bitbarista/CaffePeso/src/Display.cpp

#include "Display.h"
#include "Scale.h"
#include "FlowRate.h"
#include "BluetoothScale.h"
#include "PowerManager.h"
#include "BatteryMonitor.h"
#include <WiFi.h>
#include "WiFiManager.h"
#include <Preferences.h>

Display::Display(uint8_t sdaPin, uint8_t sclPin, Scale* scale, FlowRate* flowRate)
    : sdaPin(sdaPin), sclPin(sclPin), scalePtr(scale), flowRatePtr(flowRate), bluetoothPtr(nullptr), powerManagerPtr(nullptr), batteryPtr(nullptr),
      messageStartTime(0), messageDuration(2000), showingMessage(false), 
      timerStartTime(0), timerPausedTime(0), timerRunning(false), timerPaused(false) {
    display = new Adafruit_SSD1306(SCREEN_WIDTH, SCREEN_HEIGHT, &Wire, OLED_RESET);
}

bool Display::begin() {
    Serial.println("Initializing display...");
    
    // Initialize I2C with custom pins
    Wire.begin(sdaPin, sclPin);
    
    // Test I2C connection first with timeout
    Serial.println("Testing I2C connection to display...");
    unsigned long startTime = millis();
    const unsigned long I2C_TIMEOUT = 3000; // 3 second timeout
    
    bool i2cResponding = false;
    Wire.beginTransmission(SCREEN_ADDRESS);
    
    // Wait for I2C response with timeout
    while (millis() - startTime < I2C_TIMEOUT) {
        if (Wire.endTransmission() == 0) {
            i2cResponding = true;
            Serial.println("I2C device found at display address");
            break;
        }
        delay(100);
        Wire.beginTransmission(SCREEN_ADDRESS);
    }
    
    if (!i2cResponding) {
        Serial.println("ERROR: No I2C device found at display address");
        Serial.println("Display will be disabled - running headless mode");
        Serial.println("Check connections:");
        Serial.printf("- SDA to GPIO %d\n", sdaPin);
        Serial.printf("- SCL to GPIO %d\n", sclPin);
        Serial.println("- VCC to 3.3V");
        Serial.println("- GND to GND");
        displayConnected = false;
        return false;
    }
    
    // Initialize the display
    if (!display->begin(SSD1306_SWITCHCAPVCC, SCREEN_ADDRESS)) {
        Serial.println("ERROR: SSD1306 initialization failed");
        Serial.println("Display will be disabled - running headless mode");
        displayConnected = false;
        return false;
    }
    
    Serial.println("Display connected and initialized successfully");
    displayConnected = true;
    setupDisplay();
    
    // Show startup message in same format as welcome message
    display->clearDisplay();
    display->setTextSize(2);
    display->setTextColor(SSD1306_WHITE);
    
    String line1 = "CaffePeso";
    String line2 = "Starting";
    
    int16_t x1, y1;
    uint16_t w1, h1, w2, h2;
    
    display->getTextBounds(line1, 0, 0, &x1, &y1, &w1, &h1);
    display->getTextBounds(line2, 0, 0, &x1, &y1, &w2, &h2);
    int centerX1 = (SCREEN_WIDTH - w1) / 2;
    int centerX2 = (SCREEN_WIDTH - w2) / 2;

    display->setCursor(centerX1, 0);
    display->print(line1);
    display->setCursor(centerX2, 16);
    display->print(line2);
    
    display->display();
    
    Serial.println("SSD1306 display initialized on SDA:" + String(sdaPin) + " SCL:" + String(sclPin));
    
    return true;
}

void Display::setupDisplay() {
    // Return early if display is not connected
    if (!displayConnected) {
        return;
    }
    
    display->clearDisplay();
    display->setTextColor(SSD1306_WHITE);
    display->cp437(true); // Use full 256 char 'Code Page 437' font
}

void Display::update() {
    // Return early if display is not connected
    if (!displayConnected) {
        return;
    }
    
    // Check if message duration has elapsed
    if (showingMessage) {
        int effectiveDuration = messageDuration;
        // Use shorter duration for tared message
        if (currentMessage == "Tared message") {
            effectiveDuration = 1000; // Half of default duration for quick feedback
        }
        
        if (millis() - messageStartTime > effectiveDuration) {
            showingMessage = false;
            Serial.println("Message cleared, returning to main display");

        }
    }
    
    // Auto re-arm: tare + arm when a cup is detected after the previous shot.
    // Two detection paths:
    //   Case 1 (tap-tare workflow): user tap-tares after removing cup; fresh cup reads
    //           ≈ savedTareWeight because the tare reference is now at empty-scale.
    //   Case 2 (direct placement): user removes cup after shot (scale goes very negative),
    //           then places fresh cup directly — no tap-tare needed. Scale reads ≈ 0g
    //           because the original cup-tare reference is still intact.
    //           scaleWentNegative guards against false triggers on empty scale.
    if (scalePtr != nullptr && savedTareWeight > 5.0f && autoReArmEnabled) {
        bool activeBrew = timerRunning && !timerPaused;
        float weightNow = scalePtr->getCurrentWeight();

        // Track cup removal: set flag when scale goes deeply negative while paused
        if (timerPaused && weightNow < -(savedTareWeight * 0.5f)) {
            scaleWentNegative = true;
        }

        // Tared path: require a step change to START the stable timer.
        // Uses reArmStableSince itself as the gate:
        //   - timer not yet running + first entry into window → require step ≥ threshold
        //   - timer already running (entered via valid step) → keep it going
        //   - in window but timer never started (gradual approach) → stay blocked
        // This prevents milk being poured gradually through the cup weight from triggering re-arm.
        bool cupInWindow  = fabsf(weightNow - savedTareWeight) <= REARM_STABLE_WINDOW;
        bool prevInWindow = fabsf(prevWeightForRemoval - savedTareWeight) <= REARM_STABLE_WINDOW;
        bool cupDetectedTared;
        if (!cupInWindow) {
            cupDetectedTared = false;
        } else if (reArmStableSince != 0) {
            cupDetectedTared = true;                                     // timer running — keep going
        } else if (!prevInWindow) {
            cupDetectedTared = (weightNow - prevWeightForRemoval) >= REARM_STEP_THRESHOLD; // first entry
        } else {
            cupDetectedTared = false;                                    // gradual approach — blocked
        }
        bool cupDetectedDirect = scaleWentNegative && fabsf(weightNow) < REARM_DIRECT_WINDOW;
        bool cupDetected = cupDetectedTared || cupDetectedDirect;

        if (!activeBrew && cupDetected) {
            if (reArmStableSince == 0) reArmStableSince = millis();
            else if (millis() - reArmStableSince >= REARM_STABLE_MS) {
                reArmStableSince = 0;
                resetTimer();               // snap display to 0:00 before tare blocks
                scalePtr->tare();
                arm(savedTareWeight);
                resetTimer();               // stop that timer — auto re-arm waits for first drip
                                            // armedAutoStart is NOT cleared by resetTimer()
                showArmedMessage();
                Serial.printf("Auto re-armed: cup %.1fg detected\n", savedTareWeight);
            }
        } else {
            reArmStableSince = 0;
        }
    }

    if (!showingMessage && scalePtr != nullptr) {
        float weight = scalePtr->getCurrentWeight();

        // --- Auto-tare on vessel placement ---
        // autoTareFired is reset in resetTimer() so it fires at most once per brew cycle,
        // preventing a re-tare mid-brew when yield crosses the same threshold.
        if (autoTareEnabled) {
            float absW = fabs(weight);
            // Suppress auto-tare while the sleep/power button is held. Pressing the button
            // can transfer mechanical force through the device structure to the load cell,
            // causing a spurious reading above the threshold.
            bool sleepButtonHeld = powerManagerPtr && powerManagerPtr->isSleepTouchPressed();
            if (sleepButtonHeld) {
                autoTareStableSince = 0; // reset stability timer — don't let it accumulate while held
            } else if (weight < -2.0f) {
                autoTareStableSince = 0;
                autoTareFired = false;   // Scale went negative — vessel removed, allow auto-tare on next placement
            } else if (absW < 2.0f) {
                autoTareStableSince = 0; // Weight near zero — vessel just got tared, keep autoTareFired locked
            } else if (weight > autoTareThreshold && !autoTareFired && !timerRunning && !armedAutoStart) {
                // Only fire on positive weight — negative weight means a vessel was removed,
                // not placed. Using fabs() here caused auto-tare to trigger on large negative
                // readings (e.g. after removing a jug) which then fired again after a tap-tare.
                if (autoTareStableSince == 0) {
                    autoTareStableSince = millis();
                } else if (millis() - autoTareStableSince >= AUTO_TARE_STABLE_MS) {
                    autoTareStableSince = 0;
                    showTaringMessage();
                    scalePtr->tare();
                    resetTimer();                        // resets autoTareFired to false
                    autoTareFired = true;                // re-lock after reset so brew crossing won't re-tare
                    if (flowRatePtr) flowRatePtr->resetTimerAveraging();
                    showTaredMessage(true); // inverted to match auto re-arm visual style
                    weight = 0.0f; // reflect post-tare state immediately
                }
            } else if (weight <= autoTareThreshold) {
                autoTareStableSince = 0;
            }
        }

        // --- Post-brew idle reset ---
        // timerPaused=true after stopTimer() (timerRunning stays true); fire on paused state only.
        if (idleResetEnabled && timerPaused) {
            if (idleResetWeightStableFrom == 0) {
                idleResetWeightStableFrom = millis();
                idleResetLastWeight = weight;
            } else if (fabs(weight - idleResetLastWeight) > 0.5f) {
                idleResetWeightStableFrom = millis();
                idleResetLastWeight = weight;
            } else if (millis() - idleResetWeightStableFrom >= idleResetTimeout) {
                resetTimer();
                if (!autoReArmEnabled) {
                    // Only tare if cup re-arm is disabled — taring with cup re-arm enabled
                    // corrupts the HX711 reference and prevents re-arm from detecting the cup.
                    scalePtr->tare();
                    weight = 0.0f;
                }
                idleResetWeightStableFrom = 0;
            }
        } else if (!timerPaused) {
            idleResetWeightStableFrom = 0;
        }

        // --- Auto-zero drift correction ---
        // When idle (timer stopped) and weight has been within ±0.3g for 10s, re-tare to
        // correct slow thermal/creep drift. Keeps the zero reference accurate between brews
        // without a visible snap. The 10s window is short enough that corrections happen while
        // drift is still imperceptibly small (<0.05g typically).
        if (!timerRunning && scalePtr != nullptr) {
            if (fabsf(weight) < 0.3f && fabsf(weight) > 0.01f) {
                if (autoZeroStableSince == 0) {
                    autoZeroStableSince = millis();
                } else if (millis() - autoZeroStableSince >= AUTO_ZERO_STABLE_MS) {
                    autoZeroStableSince = 0;
                    float drift = weight;
                    scalePtr->tare();
                    weight = 0.0f;
                    Serial.printf("Auto-zero: drift corrected (was %.3fg)\n", drift);
                }
            } else {
                autoZeroStableSince = 0;
            }
        } else {
            autoZeroStableSince = 0;
        }

        // Cup removal auto-stop — if weight drops faster than any natural flow could cause,
        // the cup has been lifted; stop the timer and preserve stats
        currentWeightForCapture = weight;
        if (timerRunning && !timerPaused) {
            float weightDelta = weight - prevWeightForRemoval;
            if (prevWeightForRemoval > 5.0f && weightDelta < -CUP_REMOVAL_THRESHOLD) {
                stopTimer();
                Serial.println("Cup removal detected — timer stopped");
            }
        }
        prevWeightForRemoval = weight;

        // Armed auto-start: trigger timer when weight increases > threshold sustained 500ms.
        // Guarded against vessel placement: espresso flow rises gradually (<~0.5g per
        // 100ms cycle), whereas placing a jug/cup jumps many grams in a single cycle.
        // A step >= REARM_STEP_THRESHOLD (8g/cycle = 80g/s, impossible for coffee) is
        // treated as a placement and blocks auto-start until the weight returns to
        // baseline (vessel removed or re-tared), so e.g. weighing milk won't start the timer.
        if (armedAutoStart && !timerRunning) {
            float armStep = weight - prevWeightForArm;
            if (armStep >= REARM_STEP_THRESHOLD) {
                armBlockedByPlacement = true;          // a vessel was just placed
                armWeightAboveThresholdSince = 0;
            } else if (weight <= ARM_TRIGGER_THRESHOLD) {
                armBlockedByPlacement = false;         // back to baseline — re-allow flow detection
            }

            if (millis() - armStartedAt > ARM_TIMEOUT_MS) {
                disarm();
                Serial.println("Armed auto-start: timed out");
            } else if (weight > ARM_TRIGGER_THRESHOLD && !armBlockedByPlacement) {
                if (armWeightAboveThresholdSince == 0) {
                    armWeightAboveThresholdSince = millis();
                } else if (millis() - armWeightAboveThresholdSince >= ARM_SUSTAIN_MS) {
                    if (timerPaused) resetTimer();
                    startTimer();
                    disarm();
                    Serial.println("Armed auto-start: timer started on weight increase");
                }
            } else {
                armWeightAboveThresholdSince = 0;
            }
        }
        prevWeightForArm = weight;

        // Auto-stop on flow cessation
        if (autoStopEnabled && timerRunning && !timerPaused && flowRatePtr != nullptr) {
            float fr = flowRatePtr->getFlowRate();
            unsigned long elapsed = millis() - timerStartTime;
            if (fr > AUTO_STOP_ACTIVE_THRESHOLD) {
                autoStopFlowWasActive = true;
                autoStopBelowThresholdSince = 0;
            } else if (autoStopFlowWasActive && fr < AUTO_STOP_CEASE_THRESHOLD && elapsed > AUTO_STOP_MIN_BREW_MS) {
                if (autoStopBelowThresholdSince == 0) {
                    autoStopBelowThresholdSince = millis();
                } else if (millis() - autoStopBelowThresholdSince >= AUTO_STOP_SUSTAIN_MS) {
                    stopTimer();
                    autoStopBelowThresholdSince = 0;
                    Serial.println("Auto-stop: flow ceased");
                }
            } else if (fr >= AUTO_STOP_CEASE_THRESHOLD) {
                autoStopBelowThresholdSince = 0;
            }
        }

        // Target yield alert: invert display for 1s when approaching target yield
        if (timerRunning && !timerPaused && doseWeight > 0.5f && targetRatio > 0.0f && !alertFired) {
            float alertThreshold = doseWeight * targetRatio - 2.0f;
            if (alertThreshold > 0.0f && weight >= alertThreshold) {
                alertFired = true;
                alertFlashActive = true;
                alertFlashStart = millis();
                Serial.printf("Target yield alert: %.1fg >= threshold %.1fg\n", weight, alertThreshold);
            }
        }
        if (alertFlashActive) {
            if (millis() - alertFlashStart < ALERT_FLASH_MS) {
                display->invertDisplay(true);
            } else {
                display->invertDisplay(false);
                alertFlashActive = false;
            }
        }

        showWeightWithFlowAndTimer(weight);
    }
}

void Display::showWeight(float weight) {
    // Return early if display is not connected
    if (!displayConnected) {
        return;
    }

    if (showingMessage) return; // Don't override messages
    
    // Use the unified display showing weight, flow rate, and timer
    showWeightWithFlowAndTimer(weight);
}

void Display::showMessage(const String& message, int duration) {
    // Return early if display is not connected
    if (!displayConnected) {
        return;
    }
    
    currentMessage = message;
    messageStartTime = millis();
    messageDuration = duration; // Store the duration
    showingMessage = true;
    
    display->clearDisplay();
    display->setTextSize(1);
    display->setCursor(0, 0);
    
    // Word wrap for longer messages
    int lineHeight = 8;
    int maxCharsPerLine = 21; // For 128px width
    int currentLine = 0;
    
    for (int i = 0; i < message.length() && currentLine < 4; i += maxCharsPerLine) {
        String line = message.substring(i, min(i + maxCharsPerLine, (int)message.length()));
        display->setCursor(0, currentLine * lineHeight);
        display->print(line);
        currentLine++;
    }
    
    display->display();
}

void Display::showBatteryLowMessage(float voltage, int duration) {
    // Return early if display is not connected
    if (!displayConnected) {
        return;
    }
    
    display->clearDisplay();
    display->setTextSize(2);
    display->setTextColor(SSD1306_WHITE);
    
    String line1 = "Bat Low";
    String line2 = String(voltage, 1) + "V";
    
    int16_t x1, y1;
    uint16_t w1, h1, w2, h2;
    
    display->getTextBounds(line1, 0, 0, &x1, &y1, &w1, &h1);
    display->getTextBounds(line2, 0, 0, &x1, &y1, &w2, &h2);
    int centerX1 = (SCREEN_WIDTH - w1) / 2;
    int centerX2 = (SCREEN_WIDTH - w2) / 2;

    display->setCursor(centerX1, 0);
    display->print(line1);
    display->setCursor(centerX2, 16);
    display->print(line2);
    
    display->display();
    
    // Set message state for auto-clearing
    currentMessage = line1 + " " + line2;
    messageStartTime = millis();
    messageDuration = duration;
    showingMessage = true;
}

void Display::showSleepCountdown(int seconds) {
    // Return early if display is not connected
    if (!displayConnected) {
        return;
    }
    
    // Set message state to prevent weight display interference
    currentMessage = "Sleep countdown active";
    messageStartTime = millis();
    showingMessage = true;
    
    display->clearDisplay();
    display->setTextSize(2);
    display->setTextColor(SSD1306_WHITE);
    
    String line1 = "Sleep in";
    String line2 = String(seconds) + "...";
    
    int16_t x1, y1;
    uint16_t w1, h1, w2, h2;
    
    display->getTextBounds(line1, 0, 0, &x1, &y1, &w1, &h1);
    display->getTextBounds(line2, 0, 0, &x1, &y1, &w2, &h2);
    int centerX1 = (SCREEN_WIDTH - w1) / 2;
    int centerX2 = (SCREEN_WIDTH - w2) / 2;

    display->setCursor(centerX1, 0);
    display->print(line1);
    display->setCursor(centerX2, 16);
    display->print(line2);
    
    display->display();
}

void Display::showSleepMessage() {
    // Return early if display is not connected
    if (!displayConnected) {
        return;
    }
    
    // Set message state to prevent weight display interference
    currentMessage = "Sleep message active";
    messageStartTime = millis();
    showingMessage = true;
    
    // Large top line, small bottom line (different sizes so handled separately)
    display->clearDisplay();
    display->setTextColor(SSD1306_WHITE);
    display->setTextSize(2);
    String line1 = "Sleeping..";
    
    int16_t x1, y1;
    uint16_t w1, h1;
    display->getTextBounds(line1, 0, 0, &x1, &y1, &w1, &h1);
    int centerX1 = (SCREEN_WIDTH - w1) / 2;
    
    display->setCursor(centerX1, 0);
    display->print(line1);
    
    display->setTextSize(1);
    String line2 = "Touch to cancel";
    uint16_t w2, h2;
    display->getTextBounds(line2, 0, 0, &x1, &y1, &w2, &h2);
    int centerX2 = (SCREEN_WIDTH - w2) / 2;
    display->setCursor(centerX2, 24); // size-1 text at bottom row
    display->print(line2);
    
    display->display();
}

void Display::showGoingToSleepMessage() {
    // Return early if display is not connected
    if (!displayConnected) {
        return;
    }
    
    // Set message state to prevent weight display interference
    currentMessage = "Going to sleep message";
    messageStartTime = millis();
    showingMessage = true;
    
    display->clearDisplay();
    display->setTextSize(2);
    display->setTextColor(SSD1306_WHITE);
    String line1 = "Touch To";
    String line2 = "Wake Up";
    
    int16_t x1, y1;
    uint16_t w1, h1, w2, h2;
    
    display->getTextBounds(line1, 0, 0, &x1, &y1, &w1, &h1);
    display->getTextBounds(line2, 0, 0, &x1, &y1, &w2, &h2);
    int centerX1 = (SCREEN_WIDTH - w1) / 2;
    int centerX2 = (SCREEN_WIDTH - w2) / 2;

    display->setCursor(centerX1, 0);
    display->print(line1);
    display->setCursor(centerX2, 16);
    display->print(line2);
    
    display->display();
}

void Display::showSleepCancelledMessage() {
    // Return early if display is not connected
    if (!displayConnected) {
        return;
    }
    
    // Set message state to prevent weight display interference
    currentMessage = "Sleep cancelled message";
    messageStartTime = millis();
    showingMessage = true;
    
    display->clearDisplay();
    display->setTextSize(2);
    display->setTextColor(SSD1306_WHITE);
    String line1 = "Sleep";
    String line2 = "Cancelled";
    
    int16_t x1, y1;
    uint16_t w1, h1, w2, h2;
    
    display->getTextBounds(line1, 0, 0, &x1, &y1, &w1, &h1);
    display->getTextBounds(line2, 0, 0, &x1, &y1, &w2, &h2);
    int centerX1 = (SCREEN_WIDTH - w1) / 2;
    int centerX2 = (SCREEN_WIDTH - w2) / 2;

    display->setCursor(centerX1, 0);
    display->print(line1);
    display->setCursor(centerX2, 16);
    display->print(line2);
    
    display->display();
}

void Display::showTaringMessage() {
    // Return early if display is not connected
    if (!displayConnected) {
        return;
    }
    
    // Set message state to prevent weight display interference
    currentMessage = "Taring message";
    messageStartTime = millis();
    showingMessage = true;
    
    display->clearDisplay();
    display->setTextSize(2);
    display->setTextColor(SSD1306_WHITE);
    String line1 = "Taring";
    String line2 = "...";
    
    int16_t x1, y1;
    uint16_t w1, h1, w2, h2;
    
    display->getTextBounds(line1, 0, 0, &x1, &y1, &w1, &h1);
    display->getTextBounds(line2, 0, 0, &x1, &y1, &w2, &h2);
    int centerX1 = (SCREEN_WIDTH - w1) / 2;
    int centerX2 = (SCREEN_WIDTH - w2) / 2;

    display->setCursor(centerX1, 0);
    display->print(line1);
    display->setCursor(centerX2, 16);
    display->print(line2);
    
    display->display();
}

void Display::showReleaseMessage() {
    if (!displayConnected) return;

    currentMessage   = "Release message";
    messageStartTime = millis();
    messageDuration  = 5000; // stays until overridden by next message
    showingMessage   = true;

    display->clearDisplay();
    display->setTextSize(2);
    display->setTextColor(SSD1306_WHITE);
    String line1 = "Release";
    String line2 = "Now!";
    int16_t x1, y1;
    uint16_t w1, h1, w2, h2;
    display->getTextBounds(line1, 0, 0, &x1, &y1, &w1, &h1);
    display->getTextBounds(line2, 0, 0, &x1, &y1, &w2, &h2);
    display->setCursor((SCREEN_WIDTH - w1) / 2, 0);
    display->print(line1);
    display->setCursor((SCREEN_WIDTH - w2) / 2, 16);
    display->print(line2);
    display->display();
}

void Display::showTaredMessage(bool inverted) {
    // Return early if display is not connected
    if (!displayConnected) {
        return;
    }

    // Set message state to prevent weight display interference
    currentMessage = "Tared message";
    messageStartTime = millis();
    showingMessage = true;

    if (inverted) {
        display->fillScreen(SSD1306_WHITE);
        display->setTextColor(SSD1306_BLACK);
    } else {
        display->clearDisplay();
        display->setTextColor(SSD1306_WHITE);
    }

    // "Tared!" prominent in size 2
    display->setTextSize(2);
    String line1 = "Tared!";
    int16_t x1, y1;
    uint16_t w1, h1;
    display->getTextBounds(line1, 0, 0, &x1, &y1, &w1, &h1);
    display->setCursor((SCREEN_WIDTH - w1) / 2, 0);
    display->print(line1);

    // Hint in size 1 at bottom
    display->setTextSize(1);
    const char* hint = (savedTareWeight > 5.0f && autoReArmEnabled)
                     ? "Place cup: arm"
                     : "Hold tare: arm";
    uint16_t wh, hh;
    display->getTextBounds(hint, 0, 0, &x1, &y1, &wh, &hh);
    display->setCursor((SCREEN_WIDTH - wh) / 2, 24);
    display->print(hint);

    display->display();
    display->setTextColor(SSD1306_WHITE); // restore for subsequent draws
}


void Display::clearMessageState() {
    showingMessage = false;
    currentMessage = "";
    messageStartTime = 0;
}

void Display::showIPAddresses() {
    // Return early if display is not connected
    if (!displayConnected) {
        return;
    }

    display->clearDisplay();
    display->setTextColor(SSD1306_WHITE);

    // Top row: project name (size 2, centred)
    display->setTextSize(2);
    String name = "CaffePeso";
    int16_t x1, y1;
    uint16_t w, h;
    display->getTextBounds(name, 0, 0, &x1, &y1, &w, &h);
    display->setCursor((SCREEN_WIDTH - w) / 2, 0);
    display->print(name);

    // Bottom row: IP address (size 1, centred) — STA IP if connected, AP IP otherwise
    display->setTextSize(1);
    String ip = (WiFi.status() == WL_CONNECTED)
        ? WiFi.localIP().toString()
        : WiFi.softAPIP().toString();
    display->getTextBounds(ip, 0, 0, &x1, &y1, &w, &h);
    display->setCursor((SCREEN_WIDTH - w) / 2, 24);
    display->print(ip);

    display->display();
    delay(2000);
}

void Display::showFirstRunHint() {
    // First-run guidance: only the gesture that unlocks the hands-free workflow.
    // Draws explicit size-1 lines (showMessage's auto-wrap can't do clean line
    // breaks) but sets the message-state flags so update() auto-expires it back
    // to the live weight screen. Caller gates this on a genuine first run.
    if (!displayConnected) return;

    currentMessage   = "First run hint";
    messageStartTime = millis();
    messageDuration  = 4000;
    showingMessage   = true;

    display->clearDisplay();
    display->setTextColor(SSD1306_WHITE);
    display->setTextSize(1);
    const char* lines[] = { "Welcome to CaffePeso", "Hold the tare pad to", "tare + arm, then", "pull your first shot" };
    for (int i = 0; i < 4; i++) {
        display->setCursor(0, i * 8);
        display->print(lines[i]);
    }
    display->display();
}

void Display::clear() {
    // Return early if display is not connected
    if (!displayConnected) {
        return;
    }

    display->clearDisplay();
    display->display();
}

void Display::setBrightness(uint8_t brightness) {
    // Return early if display is not connected
    if (!displayConnected) {
        return;
    }
    
    // SSD1306 doesn't have brightness control, but we can simulate with contrast
    display->ssd1306_command(SSD1306_SETCONTRAST);
    display->ssd1306_command(brightness);
}

void Display::setBluetoothScale(BluetoothScale* bluetooth) {
    bluetoothPtr = bluetooth;
}

void Display::setPowerManager(PowerManager* powerManager) {
    powerManagerPtr = powerManager;
}

void Display::setBatteryMonitor(BatteryMonitor* battery) {
    batteryPtr = battery;
}


void Display::drawBluetoothStatus() {
    // Return early if display is not connected
    if (!displayConnected) {
        return;
    }
    
    // Only draw when connected — no indicator when scanning/disconnected
    if (bluetoothPtr && bluetoothPtr->isConnected()) {
        display->setTextSize(1);
        display->setCursor(115, 0);
        display->print("BT");
        display->drawRect(113, 0, 15, 9, SSD1306_WHITE);
    }
}

void Display::drawBatteryStatus() {
    // Return early if display is not connected or no battery monitor
    if (!displayConnected || !batteryPtr) {
        return;
    }
    
    // Get battery percentage and critical status
    int batteryPercentage = batteryPtr->getBatteryPercentage();
    bool isCritical = batteryPtr->isCriticalBattery();
    
    // Format percentage string
    String percentStr = String(batteryPercentage) + "%";
    
    // Set small text size for percentage display
    display->setTextSize(1);
    
    // For critical battery, make it flash (every 500ms)
    if (isCritical && (millis() % 1000 < 500)) {
        // Flash state - draw text with inverted colors (black text on white background)
        int16_t x1, y1;
        uint16_t textWidth, textHeight;
        display->getTextBounds(percentStr, 0, 0, &x1, &y1, &textWidth, &textHeight);
        
        // Fill background white and draw black text
        display->fillRect(0, 0, textWidth + 2, textHeight + 2, SSD1306_WHITE);
        display->setTextColor(SSD1306_BLACK);
        display->setCursor(1, 1);
        display->print(percentStr);
        display->setTextColor(SSD1306_WHITE); // Reset text color
    } else {
        // Normal percentage display in top-left corner
        display->setCursor(0, 0);
        display->print(percentStr);
    }
}

// Layout (128x32):
//   y=0..15  (16px): weight size 2, centred
//   y=16..23 ( 8px): gap
//   y=24..31 ( 8px): timer+"T" left | running ratio centre | flow right
//                    (centre ratio only when timer running and dose set;
//                     right shows final ratio when paused, flow otherwise)
void Display::showWeightWithFlowAndTimer(float weight) {
    if (!displayConnected) return;
    if (showingMessage) return;

    display->clearDisplay();

    // --- Weight: size 2, centred, top row ---
    float displayWeight = weight;
    if (weight >= -0.1f && weight <= 0.1f) displayWeight = 0.0f;
    String weightStr = String(displayWeight, weightDecimals);
    int16_t wx, wy;
    uint16_t ww, wh;
    display->setTextSize(2);
    display->getTextBounds(weightStr, 0, 0, &wx, &wy, &ww, &wh);
    display->setCursor((SCREEN_WIDTH - ww) / 2, 0);
    display->print(weightStr);

    // --- Timer string (M:SS or SS.t) ---
    float absTimer = fabs(getTimerSeconds());
    String timerStr;
    if (absTimer >= 60.0f) {
        int totalSec = (int)absTimer;
        char buf[8];
        snprintf(buf, sizeof(buf), "%d:%02d", totalSec / 60, totalSec % 60);
        timerStr = String(buf);
    } else {
        int timerSec = (int)absTimer;
        int timerDec = (int)((absTimer - timerSec) * 10 + 0.5f);
        if (timerDec >= 10) { timerSec++; timerDec = 0; }
        char buf[8];
        snprintf(buf, sizeof(buf), "%d.%d", timerSec, timerDec);
        timerStr = String(buf);
    }

    // --- Bottom row (y=24): timer size 1 left + "T"; flow/ratio size 1 right ---
    int16_t x1, y1;
    uint16_t timerW, timerH;
    display->setTextSize(1);
    display->getTextBounds(timerStr, 0, 0, &x1, &y1, &timerW, &timerH);
    display->setCursor(0, 24);
    display->print(timerStr);
    display->setCursor(timerW + 1, 24);
    display->print("T");

    // --- Centre: running ratio (timer running, dose set, weight positive) ---
    bool showRunningRatio = timerRunning && !timerPaused && doseWeight > 1.0f && weight > 0.5f;
    if (showRunningRatio) {
        char buf[10];
        snprintf(buf, sizeof(buf), "1:%.1f", weight / doseWeight);
        uint16_t w, h;
        display->getTextBounds(buf, 0, 0, &x1, &y1, &w, &h);
        display->setCursor((SCREEN_WIDTH - w) / 2, 24);
        display->print(buf);
    }

    // --- Right: flow rate (brewing) or final ratio (paused) ---
    float currentFlowRate = 0.0f;
    if (flowRatePtr != nullptr) {
        if (timerPaused && flowRatePtr->hasTimerAverage()) {
            currentFlowRate = flowRatePtr->getTimerAverageFlowRate();
        } else {
            currentFlowRate = flowRatePtr->getFlowRate();
        }
    }
    if (currentFlowRate >= -0.1f && currentFlowRate <= 0.1f) currentFlowRate = 0.0f;

    bool showFinalRatio = timerPaused && doseWeight > 1.0f && weight > 0.5f;

    if (showFinalRatio) {
        char buf[12];
        snprintf(buf, sizeof(buf), "1:%.1fR", weight / doseWeight);
        uint16_t w, h;
        display->getTextBounds(buf, 0, 0, &x1, &y1, &w, &h);
        display->setCursor(SCREEN_WIDTH - w, 24);
        display->print(buf);
    } else if (!timerRunning && !timerPaused && !armedAutoStart) {
        // Idle state — hint at how to arm.
        // If cup weight is saved and auto re-arm is on, placing the cup will arm automatically.
        // Otherwise guide the user to hold tare.
        const char* hint = (savedTareWeight > 5.0f && autoReArmEnabled)
                         ? "place cup:arm"
                         : "hold tare:arm";
        uint16_t w, h;
        display->getTextBounds(hint, 0, 0, &x1, &y1, &w, &h);
        display->setCursor(SCREEN_WIDTH - w, 24);
        display->print(hint);
    } else {
        float absFlow = fabs(currentFlowRate);
        int flowInt = (int)absFlow;
        int flowDec = (int)((absFlow - flowInt) * 10 + 0.5f);
        if (flowDec >= 10) { flowInt++; flowDec = 0; }
        char buf[12];
        snprintf(buf, sizeof(buf), currentFlowRate < 0 ? "-%d.%dF" : "%d.%dF", flowInt, flowDec);
        uint16_t w, h;
        display->getTextBounds(buf, 0, 0, &x1, &y1, &w, &h);
        display->setCursor(SCREEN_WIDTH - w, 24);
        display->print(buf);
    }

    // --- Persistent status indicators in the weight row corners (size 1, y=0) ---
    // Drawn last so they sit on top of any partial weight text overlap at the edges.
    drawBatteryStatus();    // top-left: battery %
    drawBluetoothStatus();  // top-right: BT with box when connected

    display->display();
}

// Timer management methods
void Display::startTimer() {
    if (!timerRunning) {
        // Fresh start
        timerStartTime = millis();
        timerRunning = true;
        timerPaused = false;

        // Start flow rate averaging if not already started (auto-detect starts it earlier)
        if (flowRatePtr != nullptr && !flowRatePtr->isTimerAveragingActive()) {
            flowRatePtr->startTimerAveraging();
        }
        if (powerManagerPtr != nullptr) powerManagerPtr->syncTimerRunning();
    } else if (timerPaused) {
        // Resume from paused state
        timerStartTime = millis() - timerPausedTime;
        timerPaused = false;

        // Resume flow rate averaging when timer resumes
        if (flowRatePtr != nullptr) {
            flowRatePtr->startTimerAveraging();
        }
        if (powerManagerPtr != nullptr) powerManagerPtr->syncTimerRunning();
    }
    // If timer is already running and not paused, do nothing
}

void Display::stopTimer() {
    if (timerRunning && !timerPaused) {
        timerPausedTime = millis() - timerStartTime;
        timerPaused = true;

        // Capture brew stats for shot history
        lastBrewYield = currentWeightForCapture;
        lastBrewTime  = timerPausedTime / 1000.0f;
        pendingShot   = (doseWeight > 0.5f && lastBrewYield > 5.0f && lastBrewTime > 3.0f);

        // Stop flow rate averaging when timer stops
        if (flowRatePtr != nullptr) {
            flowRatePtr->stopTimerAveraging();
        }

        // Clear armed state — brew is done, no longer waiting for first drip
        disarm();

        // Sync PowerManager so the next button tap correctly stops/resets rather than starts
        if (powerManagerPtr != nullptr) powerManagerPtr->syncTimerPaused();
    }
}

void Display::resetTimer() {
    timerStartTime = 0;
    timerPausedTime = 0;
    timerRunning = false;
    timerPaused = false;

    // autoTareFired is intentionally NOT reset here — it resets only when the scale
    // returns to near-zero, ensuring a vessel already on the scale never triggers
    // a re-tare just because the timer was reset.
    autoStopFlowWasActive = false;
    autoStopBelowThresholdSince = 0;
    idleResetWeightStableFrom = 0;
    prevWeightForRemoval = 0.0f;
    pendingShot = false;
    alertFired = false;
    if (alertFlashActive && displayConnected) {
        display->invertDisplay(false);
        alertFlashActive = false;
    }

    // Reset flow rate averaging when timer is reset
    if (flowRatePtr != nullptr) {
        flowRatePtr->resetTimerAveraging();
    }

    // Sync PowerManager state
    if (powerManagerPtr != nullptr) {
        powerManagerPtr->resetTimerState();
    }
}

void Display::notifyManualTare(float preTareWeight) {
    // A manual tare with a vessel already on the scale must arm the same one-shot
    // lock that auto-tare sets itself, otherwise auto-tare re-fires when the
    // vessel's contents later cross the threshold (e.g. milk poured into a
    // manually-tared jug). Only latch when a vessel is actually present so that
    // manually taring an empty scale still lets the next placed vessel auto-tare.
    if (preTareWeight > autoTareThreshold) {
        autoTareFired = true;
    }
}

bool Display::isTimerRunning() const {
    return timerRunning && !timerPaused;
}

bool Display::isTimerPaused() const {
    return timerPaused;
}

float Display::getTimerSeconds() const {
    if (!timerRunning) {
        return 0.0;
    } else if (timerPaused) {
        return timerPausedTime / 1000.0;
    } else {
        return (millis() - timerStartTime) / 1000.0;
    }
}


unsigned long Display::getElapsedTime() const {
    if (!timerRunning) {
        return 0;
    } else if (timerPaused) {
        return timerPausedTime;
    } else {
        return millis() - timerStartTime;
    }
}

void Display::arm(float cupWeightBeforeTare) {
    // Only update savedTareWeight when the captured weight is a plausible cup weight.
    // Guard prevents hold-tare with cup off (scale negative) from corrupting the value.
    if (cupWeightBeforeTare > 5.0f) {
        savedTareWeight = cupWeightBeforeTare;
    }
    armedAutoStart  = true;
    armStartedAt    = millis();
    armWeightAboveThresholdSince = 0;
    reArmStableSince = 0;
    scaleWentNegative = false;
    tapTaredEmpty     = false;
    armBlockedByPlacement = false; // fresh arm — clear any placement block
    prevWeightForArm = 0.0f;       // scale is tared at arm time; baseline is ~0
    armJustHappened = true;        // strobe for the arm beep (polled in main loop)
    alertFired = false; // fresh brew — reset alert

    // Persist saved cup weight across reboots
    Preferences prefs;
    if (prefs.begin("display", false)) {
        prefs.putFloat("saved_tare", savedTareWeight);
        prefs.end();
    }
    Serial.printf("Armed: cup weight = %.1fg\n", savedTareWeight);

}

void Display::disarm() {
    armedAutoStart = false;
    armWeightAboveThresholdSince = 0;
}

void Display::showArmedMessage() {
    if (!displayConnected) return;

    currentMessage    = "Armed message";
    messageStartTime  = millis();
    messageDuration   = 2500;
    showingMessage    = true;

    // Inverted display (white background) makes armed state unmistakably distinct from "Tared!"
    display->fillScreen(SSD1306_WHITE);
    display->setTextColor(SSD1306_BLACK);

    // Large "ARMED" centred on top row. Bottom row normally "Ready!", but if the
    // yield alert can't work (no dose or no ratio) nudge the user to set them —
    // otherwise the flash/Smart-Switch silently do nothing. With the shipped
    // defaults (18g / 1:2) this shows "Ready!"; it only changes if a user zeros them.
    bool yieldConfigured = doseWeight > 0.5f && targetRatio > 0.0f;
    display->setTextSize(2);
    String line1 = "ARMED";
    String line2 = yieldConfigured ? "Ready!" : "Set dose";
    int16_t x1, y1;
    uint16_t w1, h1, w2, h2;
    display->getTextBounds(line1, 0, 0, &x1, &y1, &w1, &h1);
    display->getTextBounds(line2, 0, 0, &x1, &y1, &w2, &h2);
    display->setCursor((SCREEN_WIDTH - w1) / 2, 0);
    display->print(line1);
    display->setCursor((SCREEN_WIDTH - w2) / 2, 16);
    display->print(line2);
    display->display();

    // Return display to normal after message clears (handled in update() timeout)
    display->setTextColor(SSD1306_WHITE);
}
