bitbarista/CaffePeso/include/Display.h

#ifndef DISPLAY_H
#define DISPLAY_H

#include <Wire.h>
#include <Adafruit_GFX.h>
#include <Adafruit_SSD1306.h>

class Scale; // Forward declaration
class FlowRate; // Forward declaration
class BluetoothScale; // Forward declaration
class PowerManager; // Forward declaration
class BatteryMonitor; // Forward declaration

class Display {
public:
    Display(uint8_t sdaPin, uint8_t sclPin, Scale* scale, FlowRate* flowRate);
    ~Display() { if (display) { delete display; display = nullptr; } }
    bool begin();
    bool isConnected() const { return displayConnected; } // Check if display is available
    void update();
    void showWeight(float weight);
    void showMessage(const String& message, int duration = 2000);
    void showBatteryLowMessage(float voltage, int duration = 3000);
    void showSleepCountdown(int seconds); // Show sleep countdown in large format
    void showSleepMessage(); // Show initial sleep message with big/small text format
    void showGoingToSleepMessage();   // "Touch To / Wake Up" — shown just before deep sleep
    void showSleepCancelledMessage(); // "Sleep / Cancelled" — shown when sleep is interrupted
    void showTaringMessage();         // "Taring..." — shown at 500ms hold as "keep holding" cue
    void showReleaseMessage();        // "Release!" — shown at 1500ms hold, prompts user to release
    void showTaredMessage(bool inverted = false); // "Scale / Tared!" — shown after successful tare; inverted = white bg for auto-tare
    void clearMessageState(); // Clear message state to return to weight display
    void showIPAddresses(); // Show IP address on boot (replaces "Ready" screen)
    void showFirstRunHint(); // First-run only: tells a new user the hold-tare gesture
    void clear();
    void setBrightness(uint8_t brightness);
    void setWeightDecimals(int decimals) { weightDecimals = decimals; }
    // Auto-tare on vessel placement
    void setAutoTareEnabled(bool en)       { autoTareEnabled = en; }
    void setAutoTareThreshold(float grams) { autoTareThreshold = grams; }
    bool getAutoTareEnabled() const        { return autoTareEnabled; }
    float getAutoTareThreshold() const     { return autoTareThreshold; }
    // Tell auto-tare that a MANUAL tare just happened. If a vessel was present
    // (pre-tare weight over the threshold), latch autoTareFired so auto-tare
    // won't re-fire as that vessel's contents later cross the threshold (e.g.
    // pouring milk into a manually-tared jug). preTareWeight is the reading
    // BEFORE the tare zeroed the scale.
    void notifyManualTare(float preTareWeight);

    // Post-brew idle reset
    void setIdleResetEnabled(bool en)          { idleResetEnabled = en; }
    void setIdleResetTimeout(unsigned long ms) { idleResetTimeout = ms; }
    bool getIdleResetEnabled() const           { return idleResetEnabled; }
    unsigned long getIdleResetTimeout() const  { return idleResetTimeout; }

    // Brew ratio
    void  setDoseWeight(float grams) { doseWeight = grams; }
    float getDoseWeight() const      { return doseWeight; }

    // Target yield alert
    void  setTargetRatio(float ratio) { targetRatio = ratio; }
    float getTargetRatio() const      { return targetRatio; }

    // Armed auto-start (hold tare = tare + arm)
    void  arm(float cupWeightBeforeTare); // Set arm state and save cup weight to NVS
    void  disarm();
    bool  isArmed() const              { return armedAutoStart; }
    // True exactly once after any arm/re-arm (set in arm(), clears on read).
    // Poll from the main loop to beep reliably — isArmed() edge-detection misses
    // re-arms (true->true) and arms that complete within one loop iteration.
    bool  wasArmCompleted() { bool v = armJustHappened; armJustHappened = false; return v; }
    float getSavedTareWeight() const         { return savedTareWeight; }
    void  setSavedTareWeight(float w)        { savedTareWeight = w; } // restore from NVS without arming
    void  setAutoReArmEnabled(bool en)       { autoReArmEnabled = en; }
    bool  getAutoReArmEnabled() const        { return autoReArmEnabled; }
    void  resetNegativeFlag()  { scaleWentNegative = false; }
    void  setTapTaredEmpty()   { tapTaredEmpty = true; scaleWentNegative = false; }  // tap-tare: disable direct re-arm path
    void  showArmedMessage();

    // Auto-stop on flow cessation
    void setAutoStopEnabled(bool en) { autoStopEnabled = en; }
    bool getAutoStopEnabled() const  { return autoStopEnabled; }

    // Shot stats capture (for shot history)
    bool  hasPendingShot() const   { return pendingShot; }
    float getLastBrewYield() const { return lastBrewYield; }
    float getLastBrewTime()  const { return lastBrewTime; }
    void  clearPendingShot()       { pendingShot = false; }

    // Bluetooth connection status
    void setBluetoothScale(BluetoothScale* bluetooth);
    
    // Power manager reference for timer state synchronization
    void setPowerManager(PowerManager* powerManager);
    
    // Battery monitor reference for battery status display
    void setBatteryMonitor(BatteryMonitor* battery);
    
    // Timer management
    void startTimer();
    void stopTimer();
    void resetTimer();
    bool isTimerRunning() const;
    bool isTimerPaused() const;
    float getTimerSeconds() const;
    unsigned long getElapsedTime() const; // Get current elapsed time in milliseconds
    
private:
    uint8_t sdaPin;
    uint8_t sclPin;
    Scale* scalePtr;
    FlowRate* flowRatePtr;
    BluetoothScale* bluetoothPtr;
    PowerManager* powerManagerPtr;
    BatteryMonitor* batteryPtr;
    Adafruit_SSD1306* display;
    bool displayConnected; // Track if display is actually connected
    int weightDecimals = 1; // Configurable decimal places (0, 1, or 2)

    // Cup removal auto-stop
    static constexpr float CUP_REMOVAL_THRESHOLD = 15.0f; // g drop per 100ms update = >150 g/s
    float prevWeightForRemoval = 0.0f;

    // Auto-tare on vessel placement
    bool  autoTareEnabled         = false;
    float autoTareThreshold       = 20.0f;
    bool  autoTareFired           = false;
    unsigned long autoTareStableSince = 0;
    static const unsigned long AUTO_TARE_STABLE_MS = 600;

    // Post-brew idle reset
    bool          idleResetEnabled          = false;
    unsigned long idleResetTimeout          = 30000UL;
    unsigned long idleResetWeightStableFrom = 0;
    float         idleResetLastWeight       = 0.0f;

    // Auto-zero drift correction
    unsigned long autoZeroStableSince = 0;
    static const unsigned long AUTO_ZERO_STABLE_MS = 10000;

    // Brew ratio (default 18g — popular modern-espresso dose)
    float doseWeight = 18.0f;

    // Target yield alert (default 1:2 — popular modern-espresso ratio)
    float targetRatio = 2.0f;
    bool  alertFired       = false;
    bool  alertFlashActive = false;
    unsigned long alertFlashStart = 0;
    static const unsigned long ALERT_FLASH_MS = 1000;

    // Armed auto-start
    bool  armedAutoStart   = false;
    bool  armJustHappened  = false; // strobed true for one loop on every arm/re-arm
    bool  autoReArmEnabled = true;
    float savedTareWeight  = 0.0f;
    unsigned long armStartedAt = 0;
    unsigned long armWeightAboveThresholdSince = 0;
    float prevWeightForArm = 0.0f;     // previous-cycle weight for placement-step detection
    bool  armBlockedByPlacement = false; // a vessel was placed (big step) — suppress auto-start until baseline
    bool  scaleWentNegative = false;   // set when weight < -5g; reset by arm()
    bool  tapTaredEmpty     = false;   // set by tap-tare; blocks case-1 (≈0g) until cup removed again
    unsigned long reArmStableSince  = 0;
    static constexpr float ARM_TRIGGER_THRESHOLD   = 1.0f;
    static constexpr float REARM_STABLE_WINDOW     = 5.0f;  // g — weight must be within ±5g of savedTareWeight
    static constexpr float REARM_DIRECT_WINDOW     = 20.0f; // g — direct re-arm: weight within ±20g of 0 after cup removal
    static constexpr float REARM_STEP_THRESHOLD    = 8.0f;  // g — min per-cycle step to count as cup placement (not gradual pour)
    static const unsigned long ARM_SUSTAIN_MS      = 500;
    static const unsigned long ARM_TIMEOUT_MS      = 120000; // 2 minutes
    static const unsigned long REARM_STABLE_MS     = 200;   // weight must match for 200ms to re-arm

    // Auto-stop on flow cessation (default ON — completes the hands-free pipeline)
    bool  autoStopEnabled               = true;
    bool  autoStopFlowWasActive         = false;
    unsigned long autoStopBelowThresholdSince = 0;
    static constexpr float AUTO_STOP_ACTIVE_THRESHOLD  = 1.0f;  // g/s — flow must exceed this to be "active"
    static constexpr float AUTO_STOP_CEASE_THRESHOLD   = 0.5f;  // g/s — flow below this is considered stopped
    static const unsigned long AUTO_STOP_SUSTAIN_MS    = 2000;  // flow must be below threshold for 2s
    static const unsigned long AUTO_STOP_MIN_BREW_MS   = 8000;  // don't auto-stop within first 8s of brew

    // Shot stats capture
    float currentWeightForCapture = 0.0f;
    bool  pendingShot   = false;
    float lastBrewYield = 0.0f;
    float lastBrewTime  = 0.0f;
    
    static const uint8_t SCREEN_WIDTH = 128;
    static const uint8_t SCREEN_HEIGHT = 32;
    static const uint8_t OLED_RESET = -1; // Reset pin not used
    static const uint8_t SCREEN_ADDRESS = 0x3C; // Common I2C address for SSD1306
    
    unsigned long messageStartTime;
    int messageDuration; // Store the duration for each message
    bool showingMessage;
    String currentMessage;
    
    // Timer system
    unsigned long timerStartTime;
    unsigned long timerPausedTime;
    bool timerRunning;
    bool timerPaused;
    
    void showWeightWithFlowAndTimer(float weight); // Two-row layout: weight top, timer+flow/ratio bottom
    void setupDisplay();
    void drawBluetoothStatus(); // Draw Bluetooth connection status icon
    void drawBatteryStatus(); // Draw battery status with 3-segment indicator
};

#endif
