bitbarista/CaffePeso/src/Scale.cpp

#include "Scale.h"
#include "WebServer.h"
#include "Calibration.h"
#include "FlowRate.h"

Scale::Scale(uint8_t dataPin, uint8_t clockPin, float calibrationFactor)
    : dataPin(dataPin), clockPin(clockPin), calibrationFactor(calibrationFactor), currentWeight(0.0f),
      readingIndex(0), samplesInitialized(false), previousFilteredWeight(0), medianSamples(3), averageSamples(2),
      currentFilterState(STABLE), lastBrewingActivity(0), lastStableWeight(0.0f) {
    // Initialize readings array
    for (int i = 0; i < MAX_SAMPLES; i++) {
        readings[i] = 0.0f;
    }
}

bool Scale::begin() {
    Serial.println("Starting scale initialization...");
    
    // Load calibration and check whether filter settings exist — all in one open/close
    {
        preferences.begin("scale", false);
        calibrationFactor = preferences.getFloat("calib", calibrationFactor);
        bool filterExists = preferences.isKey("brew_thresh");
        preferences.end();

        // Load filtering parameters (self-contained begin/end)
        loadFilterSettings();

        // Auto-adjust brewing threshold only if never saved by user
        if (!filterExists) {
            if (calibrationFactor < 1000) {
                brewingThreshold = 0.25f;
                Serial.println("Auto-detected 3kg load cell (low calibration factor)");
            } else if (calibrationFactor < 2500) {
                brewingThreshold = 0.15f;
                Serial.println("Auto-detected medium sensitivity load cell");
            } else {
                brewingThreshold = 0.1f;
                Serial.println("Auto-detected high sensitivity load cell (500g/2mV/V type)");
            }
            saveFilterSettings(); // self-contained begin/end, no nesting
        }
    }
    
    // Initialize HX711 with error handling
    Serial.println("Initializing HX711...");
    hx711.begin(dataPin, clockPin);
    hx711.set_scale(calibrationFactor);
    
    // Test if HX711 is responding with a timeout
    Serial.println("Testing HX711 connection...");
    unsigned long startTime = millis();
    bool testPassed = false;
    
    // Try to get a reading with 3 second timeout
    while (millis() - startTime < 3000) {
        if (hx711.is_ready()) {
            long testReading = hx711.read();
            if (testReading != 0) {  // HX711 returns 0 when not connected
                testPassed = true;
                Serial.println("HX711 test reading: " + String(testReading));
                break;
            }
        }
        delay(100);  // Small delay between attempts
    }
    
    if (testPassed) {
        Serial.println("HX711 connected successfully");
        isConnected = true;
        
        // Only tare if connection is confirmed
        Serial.println("Performing initial tare...");
        hx711.tare();
        
        Serial.println("Smart Scale filtering configured:");
        Serial.println("Brewing threshold: " + String(brewingThreshold) + "g");
        Serial.println("Stability timeout: " + String(stabilityTimeout) + "ms");
        Serial.println("Median samples (brewing): " + String(medianSamples));
        Serial.println("Average samples (stable): " + String(averageSamples));
        Serial.println("Smart filtering: ENABLED - Dynamic filter switching based on brewing activity");
        
        return true;
    } else {
        Serial.println("ERROR: HX711 not responding!");
        Serial.println("Check connections:");
        Serial.println("- VCC to 3.3V or 5V");
        Serial.println("- GND to GND");
        Serial.println("- DT to GPIO " + String(dataPin));
        Serial.println("- SCK to GPIO " + String(clockPin));
        Serial.println("- Load cell connections");
        
        isConnected = false;
        return false;
    }
}

void Scale::tare(uint8_t times) {
    if (!isConnected) {
        Serial.println("Cannot tare: HX711 not connected");
        return;
    }
    
    // Pause flow rate calculation to prevent tare operation from affecting flow rate
    if (flowRatePtr != nullptr) {
        flowRatePtr->pauseCalculation();
    }
    
    Serial.println("Taring scale...");
    // hx711.tare() busy-waits per sample with no timeout, so a stuck HX711 would
    // hang the whole device here. Confirm the chip is producing samples first; if
    // not, recover it and skip this tare rather than freezing forever.
    if (hx711.wait_ready_timeout(1000)) {
        hx711.tare(times);
        Serial.println("Tare complete");
    } else {
        recover();
        hx711Recoveries++;
        notReadySince = 0;
        Serial.println("Tare skipped: HX711 not ready, power-cycled it");
    }
    
    // Reset smart filter state after taring - return to stable mode
    currentFilterState = STABLE;
    lastBrewingActivity = 0;
    currentWeight = 0.0f;
    lastStableWeight = 0.0f;
    
    // Reinitialize sample buffer
    samplesInitialized = false;
    Serial.println("Smart filter reset to STABLE state");
    
    // Resume flow rate calculation after a short delay to ensure stable readings
    if (flowRatePtr != nullptr) {
        delay(100); // Short delay to let scale stabilize
        flowRatePtr->resumeCalculation();
        flowRatePtr->clearFlowRateBuffer(); // Clear stale readings so old flow values don't persist
    }
}

void Scale::set_scale(float factor) {
    // Only save if the calibration factor actually changed
    if (calibrationFactor != factor) {
        calibrationFactor = factor;
        hx711.set_scale(calibrationFactor);
        saveCalibration();
    }
}

void Scale::saveCalibration() {
    preferences.begin("scale", false);
    preferences.putFloat("calib", calibrationFactor);
    preferences.end();
}

void Scale::loadCalibration() {
    preferences.begin("scale", true);
    calibrationFactor = preferences.getFloat("calib", calibrationFactor);
    preferences.end();
}

float Scale::getWeight() {
    // Return 0 if HX711 is not connected
    if (!isConnected) {
        return 0.0f;
    }
    
    static unsigned long lastReadTime = 0;
    unsigned long currentTime = millis();
    
    // Read at 50Hz (every 20ms) for good responsiveness
    if (currentTime - lastReadTime < 20) {
        return currentWeight;
    }
    lastReadTime = currentTime;

    // Check if HX711 is ready before attempting to read
    if (!hx711.is_ready()) {
        // Self-heal: a healthy HX711 produces a sample every ~100ms. If it stays
        // not-ready far longer than that, an electrical glitch (e.g. espresso-machine
        // pump EMI) has likely latched it up or into power-down. Pulse it back to
        // life instead of returning a stale reading forever — that stale-0 loop is
        // exactly the "weight won't increase, scale frozen" symptom. Measure the
        // continuously-observed not-ready span (not time-since-last-read) so a busy
        // loop that skipped getWeight() can't trigger a false recovery.
        if (notReadySince == 0) {
            notReadySince = currentTime;          // first not-ready poll of this span
        } else if (currentTime - notReadySince > HX711_STALL_TIMEOUT_MS &&
                   (lastRecoverMs == 0 || currentTime - lastRecoverMs > HX711_RECOVERY_COOLDOWN_MS)) {
            // Stalled long enough AND the previous recovery has had time to settle.
            // The cooldown stops a single stall from storm-looping power-cycles
            // faster than the chip can come back.
            recover();
            hx711Recoveries++;
            lastRecoverMs = currentTime;
            notReadySince = currentTime;          // fresh window before retrying
            Serial.printf("HX711 stall recovered (power-cycled); total recoveries=%u\n", hx711Recoveries);
        }
        return currentWeight;  // Return last known value until a fresh sample arrives
    }
    notReadySince = 0; // got a fresh sample — clear the stall watchdog

    float rawReading = hx711.get_units(1);
    
    // Handle NaN or invalid readings
    if (isnan(rawReading)) {
        return currentWeight;
    }
    
    // Initialize sample buffer on first valid reading
    if (!samplesInitialized) {
        initializeSamples(rawReading);
        currentWeight = rawReading;
        lastStableWeight = rawReading;
        currentFilterState = STABLE;
        return currentWeight;
    }
    
    // Store reading in circular buffer
    readings[readingIndex] = rawReading;
    readingIndex = (readingIndex + 1) % MAX_SAMPLES;
    
    // Smart filtering based on brewing activity detection
    float weightChange = abs(rawReading - currentWeight);
    bool brewingDetected = false;
    
    // Detect brewing activity using configurable threshold
    if (currentFilterState == STABLE) {
        // Check if weight change exceeds brewing threshold
        if (weightChange > brewingThreshold) {
            brewingDetected = true;
            currentFilterState = BREWING;
            lastBrewingActivity = currentTime;
        }
    } else if (currentFilterState == BREWING) {
        // Continue monitoring for brewing activity
        if (weightChange > brewingThreshold) {
            brewingDetected = true;
            lastBrewingActivity = currentTime;
        } else {
            // Check if we should transition to stable
            if (currentTime - lastBrewingActivity > stabilityTimeout) {
                currentFilterState = TRANSITIONING;
            }
        }
    } else if (currentFilterState == TRANSITIONING) {
        // In transition phase - verify stability
        if (weightChange > brewingThreshold) {
            // Activity detected again - back to brewing
            brewingDetected = true;
            currentFilterState = BREWING;
            lastBrewingActivity = currentTime;
        } else if (currentTime - lastBrewingActivity > stabilityTimeout * 2) {
            // Extended stability confirmed - switch to stable mode
            currentFilterState = STABLE;
            lastStableWeight = currentWeight;
        }
    }
    
    // Apply appropriate filter based on current state
    float filteredWeight;
    switch (currentFilterState) {
        case BREWING:
            // Use median filter during brewing for noise rejection
            filteredWeight = medianFilter(medianSamples);
            break;
        case STABLE:
        case TRANSITIONING:
            // Use average filter for stable readings - smoother and faster
            filteredWeight = averageFilter(averageSamples);
            break;
    }
    
    // Handle rapid changes (>5g) with immediate response regardless of filter state
    if (weightChange > 5.0f) {
        filteredWeight = rawReading;
        // Reset sample buffer for immediate response
        initializeSamples(rawReading);
        // Update state appropriately
        if (currentFilterState == STABLE) {
            currentFilterState = BREWING;
            lastBrewingActivity = currentTime;
        }
    }
    
    currentWeight = filteredWeight;
    return currentWeight;
}

float Scale::getCurrentWeight() {
    return currentWeight;
}

bool Scale::isReady() {
    return isConnected && hx711.is_ready();
}

bool Scale::probeRaw(float& out) {
    // Non-blocking: only read when a conversion is already waiting, so this never
    // busy-waits on the HX711 (which is what freezes the scale on a glitch).
    if (!isConnected || !hx711.is_ready()) return false;
    out = hx711.get_value(1); // raw minus tare offset, before scale division
    return true;
}

void Scale::recover() {
    // Clear an HX711 lockup / power-down by pulsing it off then back on.
    // power-down needs PD_SCK held high >60us; power_up restarts conversions.
    hx711.power_down();
    delay(1);
    hx711.power_up();
    samplesInitialized = false; // first post-recovery reading re-seeds the filter
}

long Scale::getRawValue() {
    if (!isConnected) {
        return 0;  // Return 0 if HX711 not connected
    }
    // Called from async web handlers (calibrate, scale status). get_value() busy-
    // waits for a sample, so without a timeout a stalled HX711 would hang that task
    // forever (and racing the loop's recover() can stall it). Bail if not ready.
    if (!hx711.wait_ready_timeout(250)) {
        return 0;
    }
    return hx711.get_value(1); // Get raw value from HX711
}

void Scale::initializeSamples(float initialValue) {
    for (int i = 0; i < MAX_SAMPLES; i++) {
        readings[i] = initialValue;
    }
    samplesInitialized = true;
}

float Scale::medianFilter(int samples) {
    if (samples > MAX_SAMPLES) samples = MAX_SAMPLES;
    
    // Copy recent readings (MAX_SAMPLES is fixed, samples already bounded above)
    float temp[MAX_SAMPLES];
    for (int i = 0; i < samples; i++) {
        int idx = (readingIndex - 1 - i + MAX_SAMPLES) % MAX_SAMPLES;
        temp[i] = readings[idx];
    }
    
    // Simple bubble sort for median (efficient for small arrays)
    for (int i = 0; i < samples - 1; i++) {
        for (int j = 0; j < samples - i - 1; j++) {
            if (temp[j] > temp[j + 1]) {
                float swap = temp[j];
                temp[j] = temp[j + 1];
                temp[j + 1] = swap;
            }
        }
    }
    return temp[samples / 2]; // Return median
}

float Scale::averageFilter(int samples) {
    if (samples > MAX_SAMPLES) samples = MAX_SAMPLES;
    
    float sum = 0;
    int validSamples = 0;
    
    // Calculate average of recent samples
    for (int i = 0; i < samples; i++) {
        int idx = (readingIndex - 1 - i + MAX_SAMPLES) % MAX_SAMPLES;
        sum += readings[idx];
        validSamples++;
    }
    
    return sum / validSamples; // Return simple average without additional smoothing
}

// Filter parameter setters with validation
void Scale::setBrewingThreshold(float threshold) {
    if (threshold >= 0.05f && threshold <= 1.0f) { // Reasonable bounds
        brewingThreshold = threshold;
        saveFilterSettings();
    }
}

void Scale::setStabilityTimeout(unsigned long timeout) {
    if (timeout >= 500 && timeout <= 10000) { // 0.5-10 seconds
        stabilityTimeout = timeout;
        saveFilterSettings();
    }
}

void Scale::setMedianSamples(int samples) {
    if (samples >= 1 && samples <= MAX_SAMPLES) {
        medianSamples = samples;
        saveFilterSettings();
    }
}

void Scale::setAverageSamples(int samples) {
    if (samples >= 1 && samples <= MAX_SAMPLES) {
        averageSamples = samples;
        saveFilterSettings();
    }
}

void Scale::saveFilterSettings() {
    preferences.begin("scale", false);
    preferences.putFloat("brew_thresh", brewingThreshold);
    preferences.putULong("stab_timeout", stabilityTimeout);
    preferences.putInt("median_samples", medianSamples);
    preferences.putInt("avg_samples", averageSamples);
    preferences.end();
    Serial.println("Filter settings saved to EEPROM");
}

void Scale::loadFilterSettings() {
    preferences.begin("scale", true); // read-only
    brewingThreshold = preferences.getFloat("brew_thresh", 0.15f);
    stabilityTimeout = preferences.getULong("stab_timeout", 2000);
    medianSamples = preferences.getInt("median_samples", 3);
    averageSamples = preferences.getInt("avg_samples", 2);
    preferences.end();
}

void Scale::setFlowRatePtr(FlowRate* flowRatePtr) {
    this->flowRatePtr = flowRatePtr;
}

String Scale::getFilterState() const {
    switch (currentFilterState) {
        case STABLE: return "STABLE";
        case BREWING: return "BREWING";
        case TRANSITIONING: return "TRANSITIONING";
        default: return "UNKNOWN";
    }
}
