bitbarista/CaffePeso/include/WebServer.h

#ifndef WEBSERVER_H
#define WEBSERVER_H

#include "Scale.h"
#include "FlowRate.h"
#include "BluetoothScale.h"
#include "Display.h"
#include "BatteryMonitor.h"
#include "PowerManager.h"
#include "SmartSwitch.h"

extern float calibrationFactor;

void setupWebServer(Scale &scale, FlowRate &flowRate, BluetoothScale &bluetoothScale, Display &display, BatteryMonitor &battery, PowerManager &powerManager, SmartSwitch &smartSwitch);
void startWebServer();
void stopWebServer();
void checkPendingWiFiDisable();   // Call from loop() for OTA restart
void checkPendingShotSave(Display &display, Scale &scale); // Detect timer stop and save shot
void checkPendingBleDeinit(BluetoothScale &ble); // Call from loop() — stops BLE safely before OTA download

#endif
