bitbarista/CaffePeso/include/WiFiManager.h

#ifndef WIFI_MANAGER_H
#define WIFI_MANAGER_H

#include <WiFi.h>
#include <Preferences.h>
#include <ESPmDNS.h>

// Configuration for SuperMini antenna fix
// Set to true to enable maximum power mode for boards with poor antenna design
#define ENABLE_SUPERMINI_ANTENNA_FIX true

void setupWiFi();
void saveWiFiCredentials(const char* ssid, const char* password);
void clearWiFiCredentials(); // Clear stored WiFi credentials
void loadWiFiCredentials(char* ssid, char* password, size_t maxLen);
bool loadWiFiCredentialsFromEEPROM(); // Load and cache WiFi credentials from EEPROM
String getStoredSSID();
String getStoredPassword();
void setupWiFi(); // Setup WiFi based on saved preferences
void setupWiFiForced(); // Force WiFi setup regardless of saved state (for power optimization)
void setupmDNS(); // Setup mDNS for weighmybru.local hostname
void printWiFiStatus(); // Print detailed WiFi status for debugging
void maintainWiFi(); // Periodic WiFi maintenance to ensure AP stability
bool attemptSTAConnection(const char* ssid, const char* password); // Attempt STA connection and switch from AP mode
void switchToAPMode(); // Switch back to AP mode if STA connection fails
void applySuperMiniAntennaFix(); // Apply maximum power settings for problematic SuperMini boards
void applyAPModePowerOptimization(); // Apply power optimizations specifically for AP mode to reduce battery consumption
int getWiFiSignalStrength(); // Get current WiFi signal strength in dBm
String getWiFiSignalQuality(); // Get WiFi signal quality description
String getWiFiConnectionInfo(); // Get detailed WiFi connection information
String scanWiFiNetworks(); // Scan for available WiFi networks and return JSON

#endif
