bitbarista/CaffePeso/include/BatteryMonitor.h

#ifndef BATTERYMONITOR_H
#define BATTERYMONITOR_H

#include <Arduino.h>
#include <Preferences.h>

class BatteryMonitor {
public:
    BatteryMonitor(uint8_t batteryPin);
    void begin();
    
    // Battery readings
    float getBatteryVoltage();
    int getBatteryPercentage();
    String getBatteryStatus();  // "Full", "Good", "Low", "Critical"
    
    // Battery state indicators
    bool isCharging();  // Future expansion for charge detection
    bool isLowBattery();
    bool isCriticalBattery();
    
    // Calibration — pass actual voltage measured with a multimeter
    void calibrateVoltage(float actualVoltage);
    float getCalibrationScale() const { return calibrationScale; }
    uint8_t getBatteryPin() const { return batteryPin; }

    // Update method for periodic readings
    void update();
    
    // OLED display helper - returns battery segments (0-3)
    int getBatterySegments();
    
private:
    uint8_t batteryPin;
    Preferences preferences;
    
    // Li-ion voltage thresholds optimized for ESP32 operation (700mAh battery)
    static constexpr float BATTERY_FULL = 4.2f;      // 100% - Fresh charge
    static constexpr float BATTERY_GOOD = 4.0f;      // ~75% - Reliable ESP32 operation
    static constexpr float BATTERY_NOMINAL = 3.8f;   // ~50% - Normal operation
    static constexpr float BATTERY_LOW = 3.6f;       // ~25% - Consider charging soon
    static constexpr float BATTERY_CRITICAL = 3.4f;  // ~5%  - Charge immediately
    static constexpr float BATTERY_EMPTY = 3.2f;     // 0%   - Lower discharge threshold
    
    // Hardware configuration
    static constexpr float VOLTAGE_DIVIDER_RATIO = 2.0f;  // 100k + 100k resistors

    // Calibration and smoothing
    float calibrationScale = 1.0f;  // Multiplier to correct resistor tolerance error
    float lastVoltage = 0.0f;
    unsigned long lastUpdate = 0;
    static constexpr unsigned long UPDATE_INTERVAL = 1000; // Update every 1 second
    
    // Internal methods
    float readRawVoltage();
    void loadCalibration();
    void saveCalibration();
};

#endif
